golioth/ostentus-hw/mech/TheGolioth-5mm-1000dpi.png

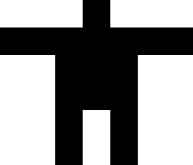
mech/TheGolioth-5mm-1000dpi.png
